celstark/camdac/camdac.py

from gpiozero import RotaryEncoder, Button
import signal
import sys
from camilladsp import CamillaClient
import RPi_I2C_driver  # Used for the 1602 display only
import threading

'''
Base code for the CamDAC

This lets you program your encoders and switchers to adjust features you'd like 
on the Camilla DSP. Key to this is that in your Camilla DSP yaml file, you have
defined a set of 5 filters called "Filt1", "Filt2" ... "Filt5" that you can
quickly tap into here. In truth, you can name them what you want in the YAML as
anything you put in here that isn't "Volume" or "VolBal" just gets passed into
Camilla

'''
# What does one click of a knob do for each control?
volume_step = 0.5
balance_step = 0.1
filt_db_step = 0.5
filt_q_step = 0.5
filt_freqs = [20, 30, 40, 50, 60, 70, 80, 90, 100, 120, 140, 160, 180, 200, 220, 240, 260, 280, 300, 400, 500, 600, 700, 800, 900, 1000, 1100, 1200, 1300, 1400,
              1500, 1750, 2000, 2250, 2500, 2750, 3000, 3250, 3500, 3750, 4000, 4500, 5000, 5500, 6000, 6500, 7000, 7500, 8000, 8500, 9000, 9500, 10000,
              10500, 11000, 11500, 12000, 13000, 14000, 15000, 16000, 17000, 18000 ]
filt_types = ['Peaking', 'Lowshelf', 'Highshelf']

bl_timeout = 10.0
DEBUG = 1
DISPLAY = 1
#symbol_act=chr(126)  # This is a right arrow --
# symbol_act=chr(94)  # This is a caret --
symbol_act=chr(255)  # Block
########################## CUSTOMIZE UNLIKELY #############################
# Setup a simple class for our encoders
class Encoder:
    def __init__(self,knob, button, nmodes=2, mode=0, name=None):
        self.knob=knob
        self.button=button
        self.mode=mode
        self.nmodes=nmodes
        self.name=name
        self.steps_last = [0] * nmodes  # We use these to allow the button to toggle modes
        self.val_last = [0.0] * nmodes
    
    def toggle_mode(self):
        # store the current readings
        self.steps_last[self.mode]=self.knob.steps
        self.val_last[self.mode]=self.knob.steps
        # toggle the mode
        # if self.mode:
        #     self.mode=0
        # else:
        #     self.mode=1
        self.mode = (self.mode+1) % self.nmodes
        # bring in the other mode values -- we actually only need to change one as it updates the other
        self.knob.steps=self.steps_last[self.mode]
    
########################## CUSTOMIZE POSSIBLE #############################
# Setup your hardware 
#
# If you're using the stock 5-encoder setup, no need to customize this part
# There are some bits like bounce_time and max_steps (sets the resolution)
# that might be worth considering. If you're using different IO pins, this
# encpins has the format A, B, SW

encpins = [ [12,13,16],
            [7,5,6],
            [9,11,8],
            [24,25,10],
            [27,22,23]]

port = 1234 # What port is Camilla's server running on? 1234 is the default

# Setup the encoder and it's mode. 
#   max_steps: Sets the range of the encoder.  Steps go from -max_steps to +max_steps as you rotate. Our dB steps
#         are set by the global above. This prevents you from having to spin like crazy to undo any massive spins
#   bounce_time: Helps prevent double-clicks when pressing the encoder in.  Min time in sec to count as a press
#   name: IMPORTANT -- This can be "Volume", "VolBal", OR the name of a filter in your CamDSP_config.yml file
#         By default, you have Filt1-Filt5 in there.  In truth, it can be any named filter in the config.
#         Note, you can, of course, override these names below when you setup the event handlers. I've set this
#         up here to show how you can easily have them be defaults
knob1 = Encoder(
    RotaryEncoder(a=encpins[0][0], b=encpins[0][1], max_steps=64),
    Button(encpins[0][2], bounce_time = 0.1),
    name="VolBal",
    nmodes=2)

knob2 = Encoder(
    RotaryEncoder(a=encpins[1][0], b=encpins[1][1], max_steps=64),
    Button(encpins[1][2], bounce_time = 0.1),
    name="Filt1",
    nmodes=4)

knob3 = Encoder(
    RotaryEncoder(a=encpins[2][0], b=encpins[2][1], max_steps=64),
    Button(encpins[2][2], bounce_time = 0.1),
    name="Filt2",
    nmodes=4)

knob4= Encoder(
    RotaryEncoder(a=encpins[3][0], b=encpins[3][1], max_steps=64),
    Button(encpins[3][2], bounce_time = 0.1),
    name="Filt3",
    nmodes=4)

knob5 = Encoder(
    RotaryEncoder(a=encpins[4][0], b=encpins[4][1], max_steps=64),
    Button(encpins[4][2], bounce_time = 0.1),
    name="Filt4",
    nmodes=4)

########################## CUSTOMIZE UNLIKELY #############################
# Callback functions to actually do things
# Note, we keep track of both the dev (an encoder wheel or a button) and the owner (object of the Encoder class -- knob1, knob2, etc)
#
# Here, we define the funtions under the hood that happen when any knob is 
# turned or any button is pressed. Don't look here first for customization


def h_toggle_mode(dev, owner=None):
    # Sent but button events -- will swap the "mode" of the dial for that encoder
    if DEBUG:
        print(f'INFO: Button -- shifting mode -- name={owner.name} was: {owner.mode} of {owner.nmodes}')
    owner.toggle_mode()
    if DISPLAY:
        enable_bl()
        if owner.name == "Volume":
            lcd.lcd_display_string(f'Volume {cdsp.volume.volume(0):+.1f} dB'.ljust(16), 1)
            lcd.lcd_display_string('',2)
        elif owner.name == "VolBal" and owner.mode == 0:
            lcd.lcd_display_string(f'Volume {cdsp.volume.volume(0):+.1f} dB'.ljust(16), 1)
            lcd.lcd_display_string('',2)
        elif owner.name == "VolBal" and owner.mode == 1:
            lcd.lcd_display_string(f'Left  {cdsp.volume.volume(1):+.1f} dB'.ljust(16), 1)
            lcd.lcd_display_string(f'Right {cdsp.volume.volume(2):+.1f} dB'.ljust(16), 2)
        else:
            BL=f"{symbol_act if owner.mode==3 else ' '}  {symbol_act if owner.mode==0 else ' '}dB   {symbol_act if owner.mode==1 else ' '}Hz  {symbol_act if owner.mode==2 else ' '}Q "
            lcd.lcd_display_string(BL.ljust(16), 2)
        

def h_adjust_knob(dev, dir=0, owner=None):
    # Top-level event handler for when a knob is rotated CW - calls appropriate function
    if DEBUG:
        print(f'INFO: Knob adjustment for {owner.name} of {dir}')
    if owner.name == "Volume":
        adjust_volume(dir)
    elif owner.name == "VolBal":
        if owner.mode == 0: 
            adjust_volume(dir)
        elif owner.mode == 1:
            adjust_balance(dev.steps)
    else:
        adjust_filter(owner,dir,owner.mode)
    if DISPLAY:
        enable_bl()

def h_reset_filter(dev, owner=None, reset_to_orig=False):
    # Top-level event handler for resetting the knob (owner) to 0 or the orig_conf value - typically on a button hold
    newval = 0
    if reset_to_orig:
        try:
            newval = orig_conf['filters'][owner.name]['parameters']['gain']
        except:
            print('ERROR: Cannot read original filter gain - setting to 0')
    if DEBUG:
        print(f'INFO: Resetting {owner.name} to {newval} dB')
    adjust_filter(owner,0,dev.mode,newval)

# Here, we send calls to Camilla
def adjust_volume(dir):
    if DEBUG:
        print(f'INFO: Adjusting volume by {volume_step * dir}')
    cdsp.volume.adjust_volume(0,volume_step * dir)
    if DISPLAY:
        lcd.lcd_display_string(f'Volume {cdsp.volume.volume(0):+.1f} dB'.ljust(16), 1)
        lcd.lcd_display_string(''.ljust(16),2)

def adjust_balance(steps):
    # Running this in a relative mode to make sure it's spot on
    # Using encoder steps, not value here
    if steps == 0: # Set both faders to 0 dB
        if DEBUG:
            print(f'INFO: Resetting balance')
        cdsp.volume.set_volume(1,0) 
        cdsp.volume.set_volume(2,0)
        # if DISPLAY:
        #     lcd.lcd_display_string('Balance: Even', 1)
        #     lcd.lcd_display_string('',2)
    elif steps > 0: # Rightwards -- dial left down
        if DEBUG:
            print(f'INFO: Balance rightwards to {-1.0 * balance_step * steps} dB {steps}')
        cdsp.volume.set_volume(1, -1.0 * balance_step * steps)
        cdsp.volume.set_volume(2,0)
        # if DISPLAY:
        #     lcd.lcd_display_string(f'Balance R: {-1.0 * balance_step * steps:.2f}', 1)
        #     lcd.lcd_display_string('',2)
    elif steps < 0: # Leftwards -- 
        if DEBUG:
            print(f'INFO: Balance leftwards to {1.0 * balance_step * steps} dB {steps}')
        cdsp.volume.set_volume(2, 1.0 * balance_step * steps)
        cdsp.volume.set_volume(1,0)
        # if DISPLAY:
        #     lcd.lcd_display_string(f'Balance L: {1.0 * balance_step * steps:.2f}', 1)
        #     lcd.lcd_display_string('',2)
    if DISPLAY:
        lcd.lcd_display_string(f'Left  {cdsp.volume.volume(1):+.1f} dB'.ljust(16), 1)
        lcd.lcd_display_string(f'Right {cdsp.volume.volume(2):+.1f} dB'.ljust(16), 2)

def adjust_filter(owner, dir=0.0, mode=0, value=None):
    # If value==None, use relative adjustments to add/sub X dB, etc
    # If value is specified, set it to that unless dir is also None.
    
    tmp_conf = cdsp.config.active()
    filt_name=owner.name
    try:
        cur_gain = tmp_conf['filters'][filt_name]['parameters']['gain']
    except:
        print(f"ERROR - Cannot retrieve paramters for {filt_name}")
        return
    cur_type = tmp_conf['filters'][filt_name]['parameters']['type']
    cur_freq = tmp_conf['filters'][filt_name]['parameters']['freq']
    cur_q =  tmp_conf['filters'][filt_name]['parameters']['q']
    
    if DEBUG:
        print(f"INFO: Adjusting {filt_name} {mode}: was -- {cur_type} {cur_freq} {cur_gain}dB, Q={cur_q}")
    if mode == 0: # dB
        cur_gain = value if value != None else cur_gain + filt_db_step * dir
    elif mode == 1: # Freq
        # Doing it this way to not need numpy
        nearest_index=min(range(len(filt_freqs)), key = lambda i: abs(filt_freqs[i]-cur_freq))
        new_index = nearest_index + int(dir)
        new_index = max(0, min(new_index, len(filt_freqs)-1))
        cur_freq = value if value != None else filt_freqs[new_index]
    elif mode == 2: #Q
        cur_q = value if value != None else cur_q + filt_q_step * dir
    elif mode == 3: # Type
        try:
            cur_index = filt_types.index(cur_type)
            new_index = cur_index + int(dir)
            new_index = max(0, min(new_index, len(filt_types)-1))
            cur_type=filt_types[new_index]
        except:
            print(f"Error - unknown current filter type {cur_type} - not changing")
            return
    
    #new_gain = value if value != None else cur_gain + eq_step * dir

    if DISPLAY:
        TL=f"{cur_type[0]} {cur_gain:+1.1f} {int(cur_freq):5} {cur_q:3.1f}"
        BL=f"{symbol_act if mode==3 else ' '}  {symbol_act if mode==0 else ' '}dB   {symbol_act if mode==1 else ' '}Hz  {symbol_act if mode==2 else ' '}Q "
        lcd.lcd_display_string(TL.ljust(16), 1)
        lcd.lcd_display_string(BL.ljust(16), 2)
        
    tmp_conf['filters'][filt_name]['parameters']['gain'] = cur_gain
    tmp_conf['filters'][filt_name]['parameters']['freq'] = cur_freq
    tmp_conf['filters'][filt_name]['parameters']['q'] = cur_q
    tmp_conf['filters'][filt_name]['parameters']['type'] = cur_type
    
    cdsp.config.set_active(tmp_conf)

# Display
if DISPLAY:
    lcd = RPi_I2C_driver.lcd()
    lcd.lcd_clear()
    lcd.backlight(0)

def disable_bl():
    global bl_status
    if bl_status:
        lcd.backlight(0)
        bl_status=0

def enable_bl():
    global bl_timer, bl_status
    try:  
        bl_timer.cancel()
    except:
        pass # We don't actually care if this fails
    if not bl_status:
        lcd.backlight(1)
    bl_timer = threading.Timer(bl_timeout,disable_bl)
    bl_timer.start()
    bl_status=1


    
    
########################## CUSTOMIZE LIKELY #############################
# Setup what the knobs and buttons actually do
#
# Let's make knob1 a volume/balance knob. We don't really need to set the name here as
# it was set by default above.  But, I'm just showing an over-ride here
knob1.name="VolBal"
knob1.knob.when_rotated_clockwise = lambda: h_adjust_knob(knob1.knob, 1, knob1)
knob1.knob.when_rotated_counter_clockwise = lambda: h_adjust_knob(knob1.knob, -1, knob1)
knob1.button.when_pressed = lambda: h_toggle_mode(knob1.button, knob1)

# Let's keep knobs 2-5 to be Filt1-4 and have their buttons, when held, reset the value
# to whatever we started the code at. That last parameter on the button.when_held controls
# if it resets to the last running or to 0.  
# Setup the event handler to call h_adjust_knob, let it know the direction, and the owner
knob2.knob.when_rotated_clockwise = lambda: h_adjust_knob(knob2.knob, 1, knob2)
knob2.knob.when_rotated_counter_clockwise = lambda: h_adjust_knob(knob2.knob, -1, knob2)
knob2.button.when_pressed = lambda: h_toggle_mode(knob2.button, knob2)
knob2.button.when_held = lambda: h_reset_filter(knob2.button,knob2,True)

knob3.knob.when_rotated_clockwise = lambda: h_adjust_knob(knob3.knob, 1, knob3)
knob3.knob.when_rotated_counter_clockwise = lambda: h_adjust_knob(knob3.knob, -1, knob3)
knob3.button.when_pressed = lambda: h_toggle_mode(knob3.button, knob3)
knob3.button.when_held = lambda: h_reset_filter(knob3.button,knob3,True)

knob4.knob.when_rotated_clockwise = lambda: h_adjust_knob(knob4.knob, 1, knob4)
knob4.knob.when_rotated_counter_clockwise = lambda: h_adjust_knob(knob4.knob, -1, knob4)
knob4.button.when_pressed = lambda: h_toggle_mode(knob4.button, knob4)
knob4.button.when_held = lambda: h_reset_filter(knob4.button,knob4,True)

# Uncomment this, for example and it'd have knob 5 be Filt5 as an override
# knob5.name="Filt5"
knob5.knob.when_rotated_clockwise = lambda: h_adjust_knob(knob5.knob, 1, knob5)
knob5.knob.when_rotated_counter_clockwise = lambda: h_adjust_knob(knob5.knob, -1, knob5)
knob5.button.when_pressed = lambda: h_toggle_mode(knob5.button, knob5)
knob5.button.when_held = lambda: h_reset_filter(knob5.button,knob5,True)


######################## CUSTOMIZE UNLIKELY #########################
bl_status=0  # Setup for backlight
bl_timer=None

# Connect to Camilla
try:
    cdsp = CamillaClient("127.0.0.1",port)
    cdsp.connect()
except:
    print("Issue connecting to CamillaDSP")
    sys.exit()
orig_conf = cdsp.config.active()  # Save this so we can reset filters to the values at start
signal.pause()
